ADBeta/TCRHMAG/Firmware/src/oled.c

/******************************************************************************
* I2C OLED Text and "Graphics" Handler, Buffer and manager library - customised
* for TCRHMAG
* Really shitty design because I ran out of patience
*
* ADBeta (c)
******************************************************************************/
#include "oled.h"
#include "lib_i2c.h"

#include <stddef.h>
#include <stdint.h>
#include <string.h>


/*** Macro Functions *********************************************************/
#define OLED_WRITE(reg, buf, size)									 \
	do {															 \
		if(i2c_write_reg(_oled_dev, (reg), (buf), (size)) != I2C_OK) \
			return OLED_I2C_FAILED;									 \
	} while(0)

#define OLED_PRINT_8X8_CENTERED(row, str)                            \
	do {                                                             \
		uint8_t _x = (OLED_WIDTH - ((sizeof(str) - 1) * 8)) / 2;            \
		font8x8_to_framebuffer((str), &_oled_buffer[(row)][_x]);     \
	} while (0)



/*** Static Variables ********************************************************/
/// @brief Pointer to the OLED I2C Device for later use - use init() to set
static const i2c_device_t *_oled_dev = NULL;

// Framebuffer (page-based)
static uint8_t _oled_buffer[OLED_PAGES][OLED_WIDTH];


/*** Font Data ***************************************************************/
/// @brief 6x8 Battery Percentage Icon font ///////////////////////////////////
static const uint8_t font6x8_battperc_data[][6] = {
	{0x3C, 0xE7, 0x81, 0xBD, 0xBD, 0xBD},     // Filled Top Bar
	{0x3C, 0xE7, 0x81, 0x81, 0x81, 0x81},     // Empty Top Bar
	{0xBD, 0xBD, 0xBD, 0xBD, 0xBD, 0xBD},     // Filled Middle Bar
	{0x81, 0x81, 0x81, 0x81, 0x81, 0x81},     // Empty Middle Bar
	{0xBD, 0xBD, 0xBD, 0xBD, 0x81, 0xFF},     // Filled Bottom Bar
	{0x81, 0x81, 0x81, 0x81, 0x81, 0xFF}      // Empty Bottom Bar
};

#define FONT6x8_BATTPERC_FILLED_TOP      font6x8_battperc_data[0]
#define FONT6x8_BATTPERC_EMPTY_TOP       font6x8_battperc_data[1]
#define FONT6x8_BATTPERC_FILLED_MIDDLE   font6x8_battperc_data[2]
#define FONT6x8_BATTPERC_EMPTY_MIDDLE    font6x8_battperc_data[3]
#define FONT6x8_BATTPERC_FILLED_BOTTOM   font6x8_battperc_data[4]
#define FONT6x8_BATTPERC_EMPTY_BOTTOM    font6x8_battperc_data[5]



/// @brief 8x8 Font ///////////////////////////////////////////////////////////
static const uint8_t font8x8_data[][8] = {
	{0x00, 0x00, 0x00, 0x00, 0x00, 0x00, 0x00, 0x00},   // ' '
	{0x46, 0x66, 0x30, 0x18, 0x0C, 0x66, 0x62, 0x00},   // '%'
	{0x00, 0x00, 0x60, 0x60, 0x00, 0x00, 0x00, 0x00},   // '.'
	{0x3E, 0x7F, 0x71, 0x59, 0x4D, 0x7F, 0x3E, 0x00},	// '0'
	{0x40, 0x42, 0x7F, 0x7F, 0x40, 0x40, 0x00, 0x00},	// '1'
	{0x62, 0x73, 0x59, 0x49, 0x6F, 0x66, 0x00, 0x00},	// '2'
	{0x22, 0x63, 0x49, 0x49, 0x7F, 0x36, 0x00, 0x00},	// '3'
	{0x18, 0x1C, 0x16, 0x53, 0x7F, 0x7F, 0x50, 0x00},	// '4'
	{0x27, 0x67, 0x45, 0x45, 0x7D, 0x39, 0x00, 0x00},	// '5'
	{0x3C, 0x7E, 0x4B, 0x49, 0x79, 0x30, 0x00, 0x00},	// '6'
	{0x03, 0x03, 0x71, 0x79, 0x0F, 0x07, 0x00, 0x00},	// '7'
	{0x36, 0x7F, 0x49, 0x49, 0x7F, 0x36, 0x00, 0x00},	// '8'
	{0x06, 0x4F, 0x49, 0x69, 0x3F, 0x1E, 0x00, 0x00},	// '9'
	{0x00, 0x00, 0x66, 0x66, 0x00, 0x00, 0x00, 0x00},	// ':'
	{0x00, 0x80, 0xE6, 0x66, 0x00, 0x00, 0x00, 0x00},	// ';'
	{0x08, 0x1C, 0x36, 0x63, 0x41, 0x00, 0x00, 0x00},	// '<'
	{0x24, 0x24, 0x24, 0x24, 0x24, 0x24, 0x00, 0x00},	// '='
	{0x00, 0x41, 0x63, 0x36, 0x1C, 0x08, 0x00, 0x00},	// '>'
	{0x02, 0x03, 0x51, 0x59, 0x0F, 0x06, 0x00, 0x00},	// '?'
	{0x3E, 0x7F, 0x41, 0x5D, 0x5D, 0x1F, 0x1E, 0x00},	// '@'
	{0x7C, 0x7E, 0x13, 0x13, 0x7E, 0x7C, 0x00, 0x00},	// 'A'
	{0x41, 0x7F, 0x7F, 0x49, 0x49, 0x7F, 0x36, 0x00},	// 'B'
	{0x1C, 0x3E, 0x63, 0x41, 0x41, 0x63, 0x22, 0x00},	// 'C'
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
	{0x0000, 0x0000, 0x0000, 0x0000, 0x0000, 0x0000, 0x6002, 0x6002, 0x7FFE, 0x7FFE, 0x0000, 0x0000, 0x0000, 0x0000, 0x0000, 0x0000} 	// ']'
};

static const char font16_16_lut[] = {" .0123456789CF`[]"};



/*** Static Functions ********************************************************/
/// @brief Copies Data from the 8x8 font to the given data buffer pointer
/// @param str, string to append
/// @param ptr, Pointer to the data buffers position to append to
/// @return None
static void font8x8_to_framebuffer(const char *str, uint8_t *ptr)
{
	if(str == NULL || ptr == NULL) return;
	
	while(*str)
	{
		// Find the desired char in the small font LUT (incriment str too)
		const char *lut_ptr = strchr(font8x8_lut, *str++);
		if(lut_ptr == NULL) continue;
		
		// Copy the font data for the given char to the framebuffer
		memcpy(ptr, font8x8_data[lut_ptr - font8x8_lut], sizeof(font8x8_data[0]));
		ptr += sizeof(font8x8_data[0]);
	}
}


/// @brief Copies Data from the 16x16 font to the given data buffer pointer
/// @param str, string to append
/// @param ptr, Pointer to the data buffers position to append to
/// @return None
/// NOTE: This has no overflow protection, because I lost the will to care. 
/// Don't be a dumbshit when using this function :)
static void font16x16_to_framebuffer(const char *str, uint8_t *ptr)
{
	if(str == NULL || ptr == NULL) return;


	#define GLYPH_ROWS (sizeof(font16x16_data[0]) / sizeof(font16x16_data[0][0]))
	while(*str)
	{
		// Find the desired char in the large font LUT (incriment str too)
		const char *lut_ptr = strchr(font16_16_lut, *str++);
		if(lut_ptr == NULL) continue;
		
		// Copy the font data for the given char to the framebuffer
		// Draw data[0] above data[1], etc with data[2] above data[3]
		const uint16_t *glyph = font16x16_data[lut_ptr - font16_16_lut];
		for(uint8_t line = 0; line < GLYPH_ROWS; line++)
		{
			ptr[line]              = (uint8_t)(glyph[line] & 0xFF);
			ptr[line + OLED_WIDTH] = (uint8_t)(glyph[line] >> 8);
		}


		ptr += GLYPH_ROWS;
	}
}


/// @brief Converts a given millivolt/milliamp value to a 2 decimal place
/// formatted string at the given pointer
/// @param val, Milli[x] range value
/// @param str, pointer to the first char of the string to append to
/// @return None
static void append_formatted_2dp_string(const uint16_t val, char *str)
{
	uint16_t whole = val / 1000;          // volts
	uint16_t frac  = (val % 1000) / 10;   // hundredths of a volt

	str[0] = (whole / 10) + '0';
	str[1] = (whole % 10) + '0';
	str[2] = '.';
	str[3] = (frac / 10) + '0';
	str[4] = (frac % 10) + '0';
}


/// @brief Converts a given value to a 3 digit, zero padded string
/// @param val, value to convert (999 max)
/// @param str, pointer to the first char of the string to append to
static void append_padded_3digit_string(const uint16_t val, char *str)
{
	str[0] = '0' + ((val / 100) % 10);
	str[1] = '0' + ((val / 10)  % 10);
	str[2] = '0' +  (val % 10);	
}



/*** Hardware Function Definitions *******************************************/
oled_err_t oled_init(const i2c_device_t *dev)
{
	if(dev == NULL) return OLED_INVALID_INPUT;

	// Set the static i2c device value to the given device
	_oled_dev = dev;

	const uint8_t init_arr[] = {
		0xAE,			// Display OFF
		0xD5, 0xF0,		// Clock
		0xA8, 0x3F,		// Multiplex (64)
		0xD3, 0x00,		// Offset
		0x40,			// Start line
		0x8D, 0x14,		// Charge pump
		0x20, 0x00,		// Horizontal addressing
		0xA1,			// Segment remap
		0xC8,			// COM scan dec
		0xDA, 0x12,		// COM pins
		0x81, 0x7F,		// Contrast
		0xD9, 0x22,		// Pre-charge
		0xDB, 0x40,		// VCOM detect
		0xA4,			// Resume RAM
		0xA6,			// Normal display
		0xAF			// Display ON
	};
	
	// Write the Initialisation Array to the Display
	OLED_WRITE(OLED_REG_COMMAND, init_arr,  sizeof(init_arr));
	
	return OLED_OK;
}


oled_err_t oled_set_cursor(const uint8_t x, const uint8_t y)
{
	if(x >= OLED_WIDTH || y >= OLED_PAGES) 
		return OLED_INVALID_INPUT;

	uint8_t pos_arr[3] = { (0xB0 | y), 
						   (0x00 | (x & 0x0F)), 
						   (0x10 | (x >> 4)) };
	// Set Page Address
	OLED_WRITE(OLED_REG_COMMAND, &pos_arr[0], 1);
	// Set lower column address
	OLED_WRITE(OLED_REG_COMMAND, &pos_arr[1], 1);
	// Set upper column address
	OLED_WRITE(OLED_REG_COMMAND, &pos_arr[2], 1);

	return OLED_OK;
}


oled_err_t oled_update(void)
{
	if(_oled_dev == NULL) return OLED_UNSET_DEVICE;
	
	// Write the OLED Display Data
	for(int page = 0; page < OLED_PAGES; page++)
	{	
		oled_set_cursor(0, page);
		OLED_WRITE(OLED_REG_DISPLAY_START, _oled_buffer[page], OLED_WIDTH);
	}

	return OLED_OK;
}




/*** Drawing API Functions ***************************************************/
void oled_draw_boot_screen(void)
{
	OLED_PRINT_8X8_CENTERED(2, "BOOTING");
	OLED_PRINT_8X8_CENTERED(3, "TCRHMAG");
	OLED_PRINT_8X8_CENTERED(4, "V1.2");
}


void oled_draw_error_undervoltage_screen(void)
{
	OLED_PRINT_8X8_CENTERED(2, "~~~ ERROR ~~~");
	OLED_PRINT_8X8_CENTERED(4, "BATTERY");
	OLED_PRINT_8X8_CENTERED(5, "VOLTAGE LOW");
}


void oled_draw_error_overcurrent_screen(void)
{
	OLED_PRINT_8X8_CENTERED(2, "~~~ ERROR ~~~");
	OLED_PRINT_8X8_CENTERED(4, "BATTERY");
	OLED_PRINT_8X8_CENTERED(5, "OVERCURRENT");
}


void oled_clear_display(void)
{
	memset(&_oled_buffer[0][0], 0x00, OLED_WIDTH * OLED_PAGES);
}


void oled_clear_battery_info(void)
{
	memset(&_oled_buffer[0][0], 0x00, OLED_WIDTH);
}


void oled_draw_battery_current(const uint16_t batt_ma)
{
	static char current_str[7] = "00.00A";
	append_formatted_2dp_string(batt_ma, &current_str[0]);
	font8x8_to_framebuffer(current_str, (uint8_t *)&_oled_buffer[0][0]);
}


void oled_draw_battery_voltage(const uint16_t batt_mv)
{
	static char voltage_str[7] = "00.00V";
	append_formatted_2dp_string(batt_mv, &voltage_str[0]);
	font8x8_to_framebuffer(voltage_str, (uint8_t *)&_oled_buffer[0][82]);
}


void oled_draw_battery_percent(const uint8_t batt_perc)
{
	const uint8_t *font_ptr = NULL;

	font_ptr = (batt_perc >= 75) ? FONT6x8_BATTPERC_FILLED_TOP : FONT6x8_BATTPERC_EMPTY_TOP;
	memcpy(&_oled_buffer[0][110], font_ptr, 6);

	font_ptr = (batt_perc >= 50) ? FONT6x8_BATTPERC_FILLED_MIDDLE : FONT6x8_BATTPERC_EMPTY_MIDDLE;
	memcpy(&_oled_buffer[0][116], font_ptr, 6);

	font_ptr = (batt_perc >= 25) ? FONT6x8_BATTPERC_FILLED_BOTTOM : FONT6x8_BATTPERC_EMPTY_BOTTOM;
	memcpy(&_oled_buffer[0][122], font_ptr, 6);
}


void oled_draw_temperature(const uint16_t target, const uint16_t actual)
{
	static char target_str[6] = "000`C";
	static char actual_str[6] = "000`C";

	append_padded_3digit_string(target, target_str);
	append_padded_3digit_string(actual, actual_str);

	font8x8_to_framebuffer("~~~~ TARGET ~~~~",  &_oled_buffer[1][0]);	
	font16x16_to_framebuffer(target_str,        &_oled_buffer[2][24]);
	font8x8_to_framebuffer("~~~~ ACTUAL ~~~~",  &_oled_buffer[5][0]);
	font16x16_to_framebuffer(actual_str,        &_oled_buffer[6][24]);
}

void oled_draw_heater_state(const bool heater_on)
{
	static const uint8_t icon_on[8] =  { 0x3C, 0x7E, 0xFF, 0xFF, 0xFF, 0xFF, 0x7E, 0x3C };
	static const uint8_t icon_off[8] = { 0x3C, 0x66, 0xC3, 0x81, 0x81, 0xC3, 0x66, 0x3C };

	const uint8_t *ptr = heater_on ? icon_on : icon_off;
	memcpy(&_oled_buffer[6][120], ptr, 8);	
}
