ADBeta/TCRHMAG/Firmware/src/thermistor_lut.h

#ifndef THERMISTOR_LUT_H
#define THERMISTOR_LUT_H


typedef struct {
	uint16_t temp_c;    // Temperate Sample (Degrees Celsius)
	uint16_t adc;       // MCU ADC Value at given temperature
} thermistor_pair_t;

// NTC Thermistor LUT assuming Rf of 4700R, VCC of 5.0V and ADC with 1023 Counts
static const thermistor_pair_t thermistor_pair[] __attribute__((section(".rodata"))) = {
	{  0,	1009},
	{  4,	1006},
	{  8,	1002},
	{ 12,	997},
	{ 16,	992},
	{ 20,	986},
	{ 24,	979},
	{ 28,	971},
	{ 32,	962},
	{ 36,	951},
	{ 40,	940},
	{ 44,	927},
	{ 48,	912},
	{ 52,	896},
	{ 56,	879},
	{ 60,	860},
	{ 64,	840},
	{ 68,	819},
	{ 72,	796},
	{ 76,	772},
	{ 80,	747},
	{ 84,	721},
	{ 88,	694},
	{ 92,	667},
	{ 96,	639},
	{100,	611},
	{104,	583},
	{108,	556},
	{112,	528},
	{116,	501},
	{120,	475},
	{124,	449},
	{128,	424},
	{132,	400},
	{136,	377},
	{140,	355},
	{144,	335},
	{148,	315},
	{152,	296},
	{156,	278},
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
};


#define THERMISTOR_PAIR_ENTRIES \
	(sizeof(thermistor_pair) / sizeof(thermistor_pair[0]))

#endif
